Liolaeus/lio46/ergogen/output/outlines/plate_right.dxf

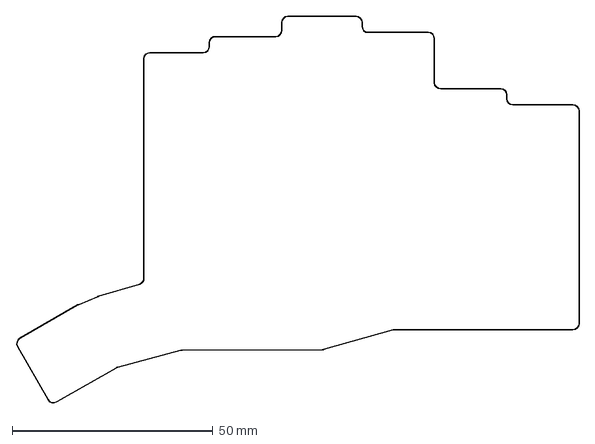
[picture p22: CAD file, 2025-01-01]
ergogen/output/outlines/plate_right.dxf
140.1 x 96.3 mm
