Liolaeus/lio46/ergogen/output/outlines/plate_left.dxf

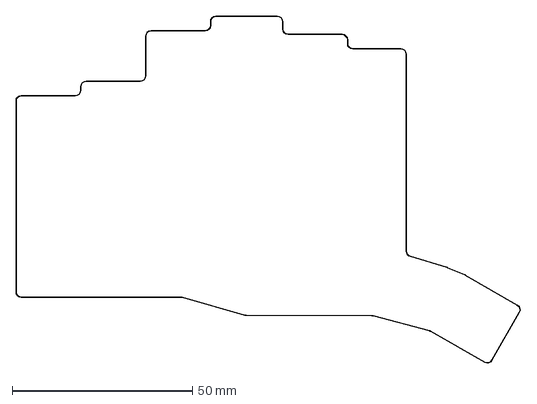
[picture p23: CAD file, 2025-01-01]
ergogen/output/outlines/plate_left.dxf
140.1 x 96.3 mm
