Liolaeus/lio46/ergogen/output/outlines/controller.dxf

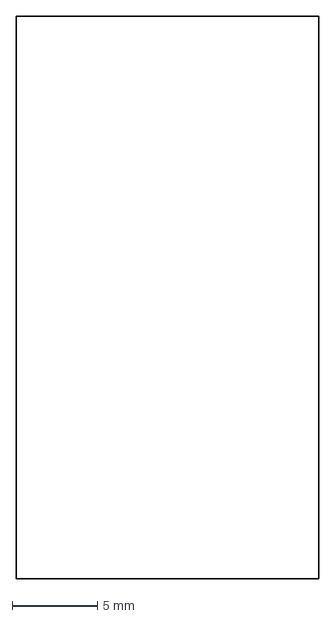
[picture p24: CAD file, 2024-11-16]
ergogen/output/outlines/controller.dxf
17.8 x 33.0 mm
